dilshan/24ch-usb-high-voltage-driver/resources/sample-driver-interface/sample-driver-interface.kicad_pcb

## KiCad design pcbs/chips-34.kicad_pcb

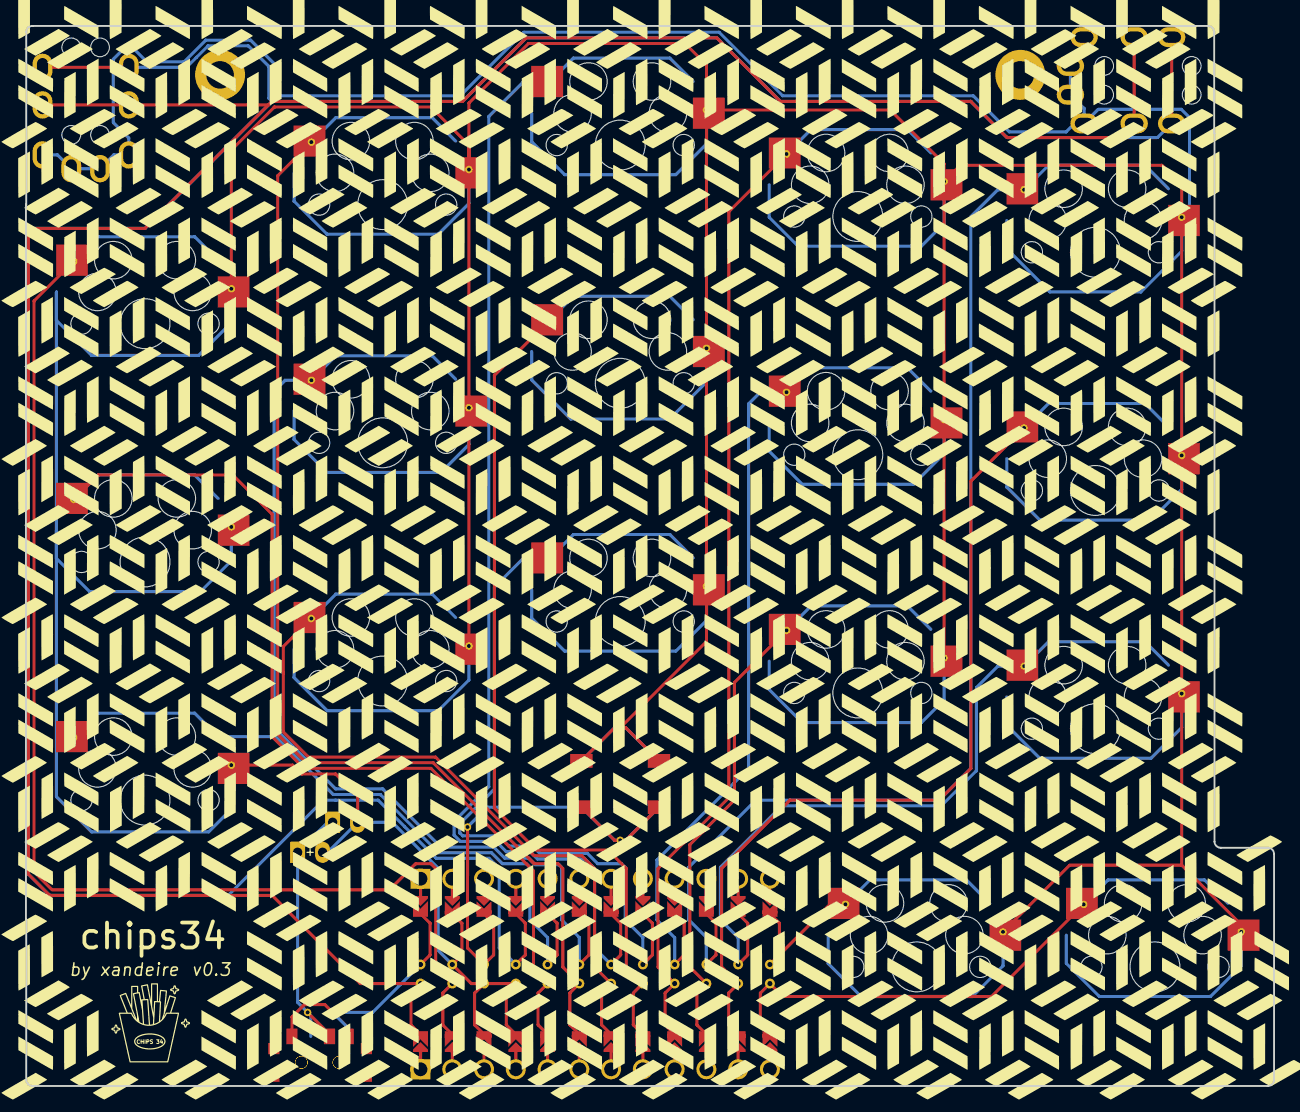
[picture p6: board chips-34.kicad_pcb from above]

Board: 2 copper layers, 99.8 x 84.8 mm, 26 parts (0 on the bottom side), 23 nets.

Parts:
B1, B2: SW_TACT_ALPS_SKQGABE010
JST1, JST2: JST_PH_S2B-PH-K_02x2.00mm_Angled
MCU1: ProMicro
S1, S2, S3, S4, S5, S6, S7, S8, S9, S10, S11, S12, S13, S14, S15, S16, S17: MX
T1, T2: SPDT_C128955
TRRS1, TRRS2: TRRS-PJ-320A-dual

Connections:
BAT: JST1.1, JST2.1, T1.2, T2.2
GND: B1.2, B2.2, JST1.2, JST2.2, MCU1.2, MCU1.21, MCU1.22, S1.1, S2.1, S3.1, S4.1, S5.1, S6.1, S7.1, S8.1, S9.1, S10.1, S11.1, S12.1, S13.1, S14.1, S15.1, S16.1, S17.1, TRRS1.1, TRRS1.2, TRRS2.1, TRRS2.2
P1: MCU1.24, TRRS1.3, TRRS2.3
RAW: MCU1.1, T1.1, T2.1
RST: B1.1, B2.1, MCU1.3
VCC: MCU1.4, TRRS1.4, TRRS2.4
matrix_index_bottom: MCU1.15, S10.2
matrix_index_home: MCU1.9, S11.2
matrix_index_top: MCU1.16, S12.2
matrix_inner_bottom: MCU1.11, S13.2
matrix_inner_home: MCU1.14, S14.2
matrix_inner_top: MCU1.10, S15.2
matrix_middle_bottom: MCU1.8, S7.2
matrix_middle_home: MCU1.17, S8.2
matrix_middle_top: MCU1.7, S9.2
matrix_pinky_bottom: MCU1.5, S1.2
matrix_pinky_home: MCU1.20, S2.2
matrix_pinky_top: MCU1.23, S3.2
matrix_ring_bottom: MCU1.18, S4.2
matrix_ring_home: MCU1.6, S5.2
matrix_ring_top: MCU1.19, S6.2
thumb_resting: MCU1.13, S16.2
thumb_squeeze: MCU1.12, S17.2
