dilshan/24ch-usb-high-voltage-driver/Firmware/include/stc15.h

//-------------------------------------------------------------
// STC15 series header for SDCC.
// 
// Based on STC15series MCU Data Sheet - 2015/10/10.
// Last updated: Dilshan Jayakody [14th Jan 2021]
//
// Update log:
// [14/01/2021] - Initial version - Dilshan Jayakody.
//-------------------------------------------------------------

#ifndef STC15W_MAIN_H
#define STC15W_MAIN_H

#include "stc15reg.h"
#include "inst.h"
#include "interrupt.h"

#include "sysmap.h"
#include "timer.h"
#include "uart.h"
#include "adc.h"
#include "iap.h"
#include "spi.h"
#include "pcapwm.h"

#endif /* STC15W_MAIN_H */
